profdc9/GuitarPico/StompBox/StompBox.png

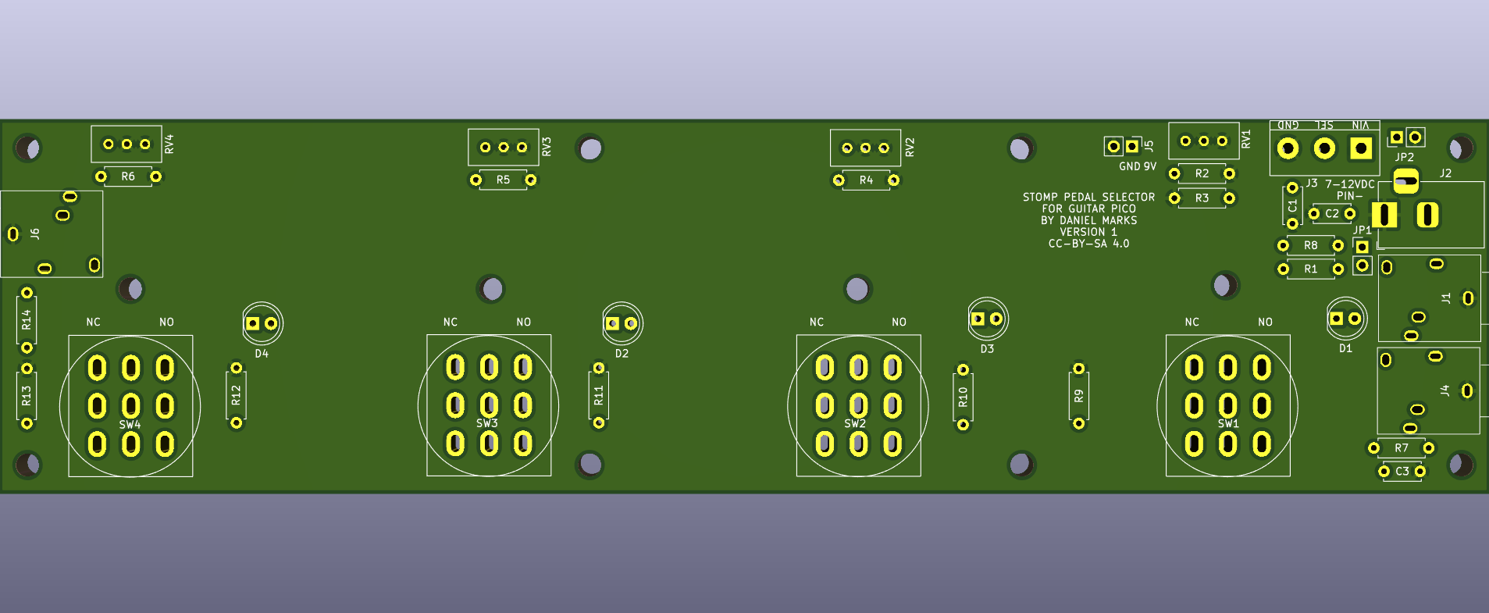
StompBox/StompBox.png
